thermseekr/esp-poe-2rl/V1/eumesmo-poe-2rl-v1.6.png

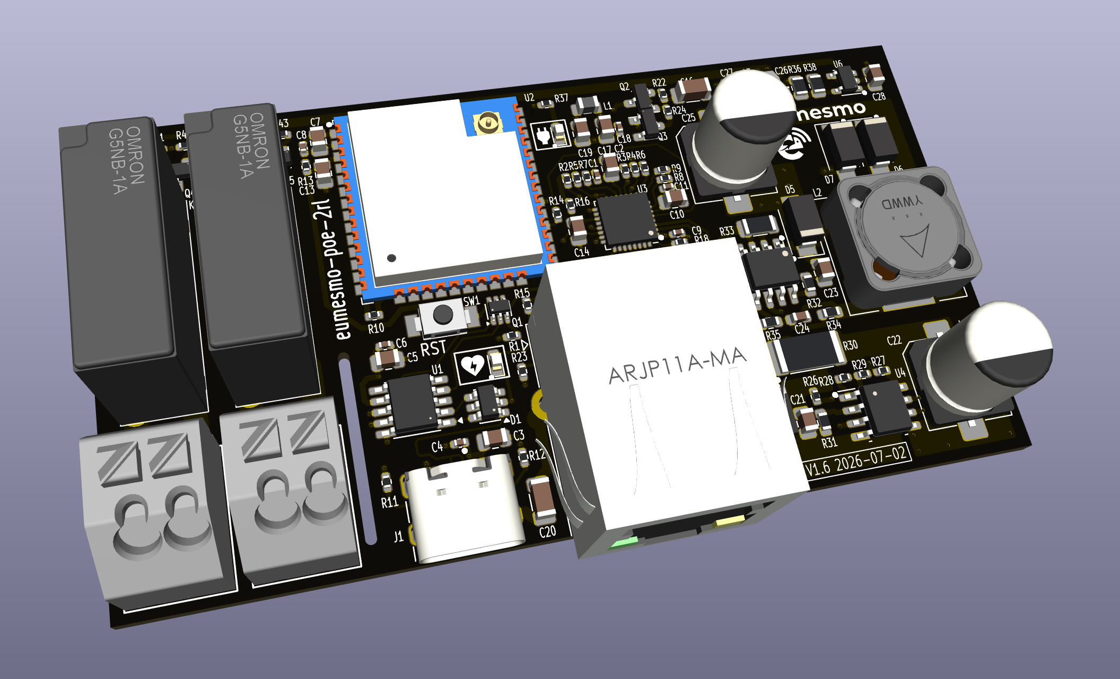
V1/eumesmo-poe-2rl-v1.6.png
